silicagel777/SuperClock/src/driver/rtc/ds3231.h

#pragma once

#include <driver/calib/icalib.h>
#include <driver/rtc/irtc.h>
#include <driver/temp/itemp.h>

class I2C;

class Ds3231 : public IRtc, public ITemp, public ICalib {
public:
  Ds3231(I2C &i2c);
  uint8_t readTime(RtcTime &time) override;
  uint8_t setTime(const RtcTime &time) override;
  uint8_t readTemp(TempValue &temp) override;
  uint8_t readCalib(int8_t &calib) override;
  uint8_t setCalib(int8_t calib) override;

private:
  Ds3231(const Ds3231 &) = delete;
  void operator=(const Ds3231 &) = delete;
  static constexpr uint8_t c_busAddr = 0x68;
  I2C &m_i2c;
};
